Gabmax4/esp-webserver-battery-csv/Graficas bateria/Analis de las graficas/lectura-bateria.pdf

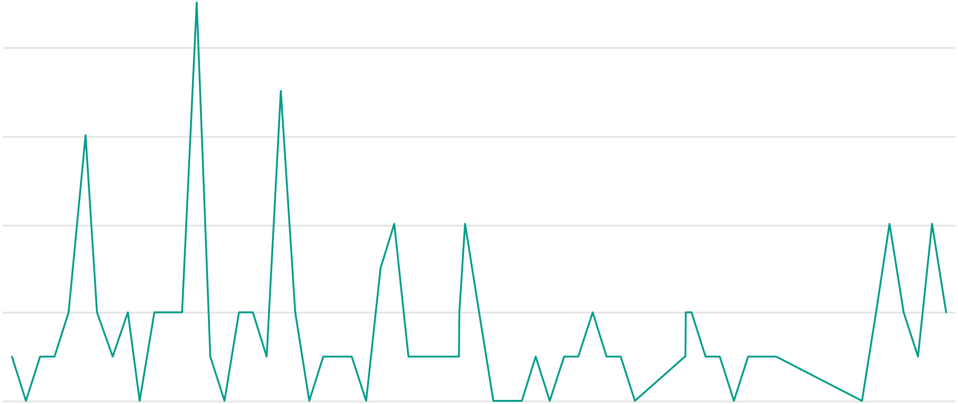
[picture p11: figure]

Tiempo

B

a

t

e

ria

## Lectura Bateria

22:43:30 | 22:43:45 | 22:44:00 | 22:44:15 | 22:44:30

616

618

620

622

624

626

628
