Gabmax4/esp-webserver-battery-csv/Graficas bateria/Carga de bateria/lectura-bateria (1).jpeg

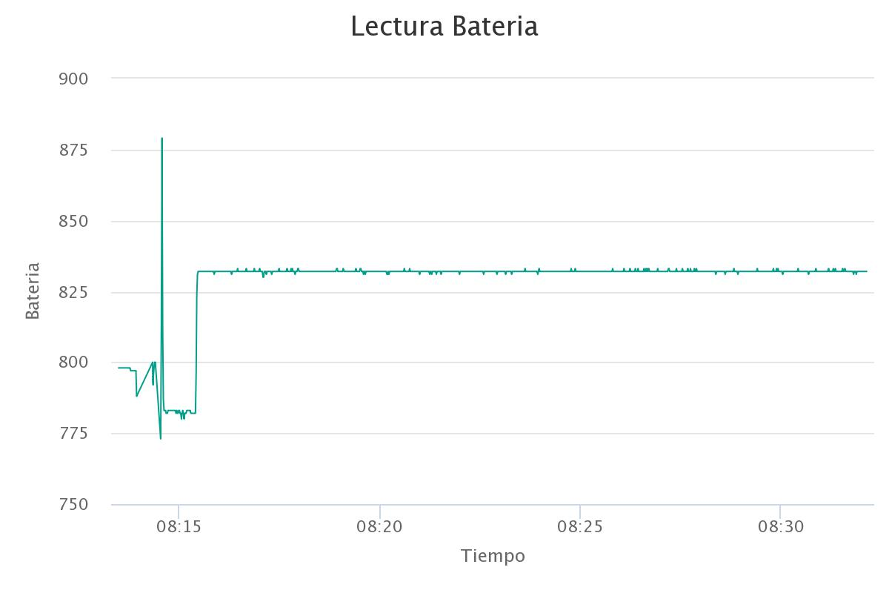
Graficas bateria/Carga de bateria/lectura-bateria (1).jpeg
