Gabmax4/esp-webserver-battery-csv/Graficas bateria/Carga de bateria/lectura-bateria.jpeg

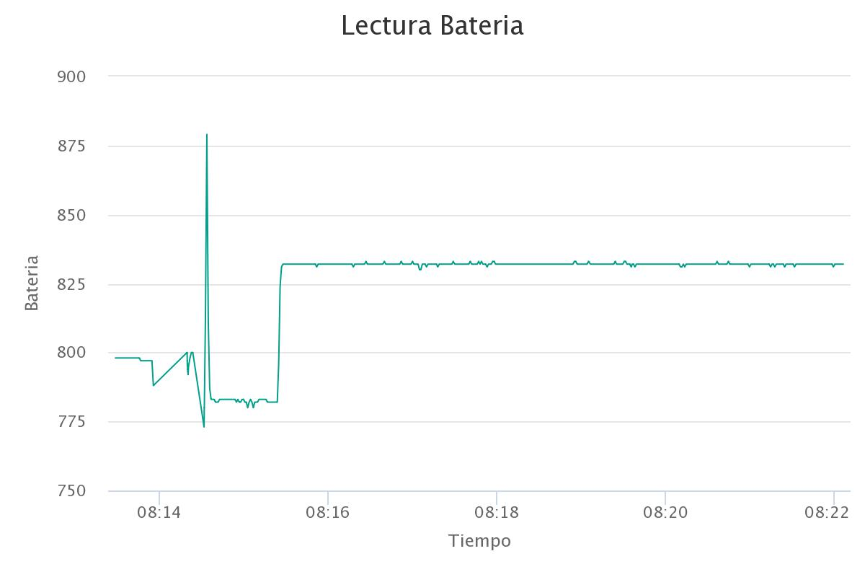
Graficas bateria/Carga de bateria/lectura-bateria.jpeg
