Gabmax4/esp-webserver-battery-csv/Simulacion 3D/Cargador-De-Pulseras.png

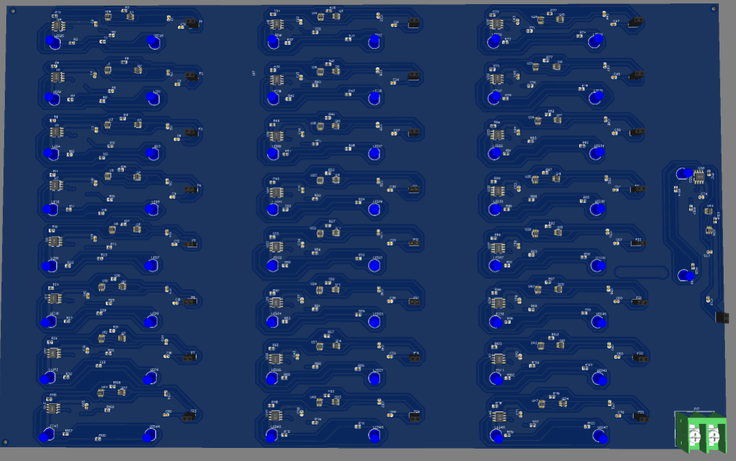
Simulacion 3D/Cargador-De-Pulseras.png
