Gabmax4/esp-webserver-battery-csv/Simulacion 3D/Escamatico-De-Pulsera.png

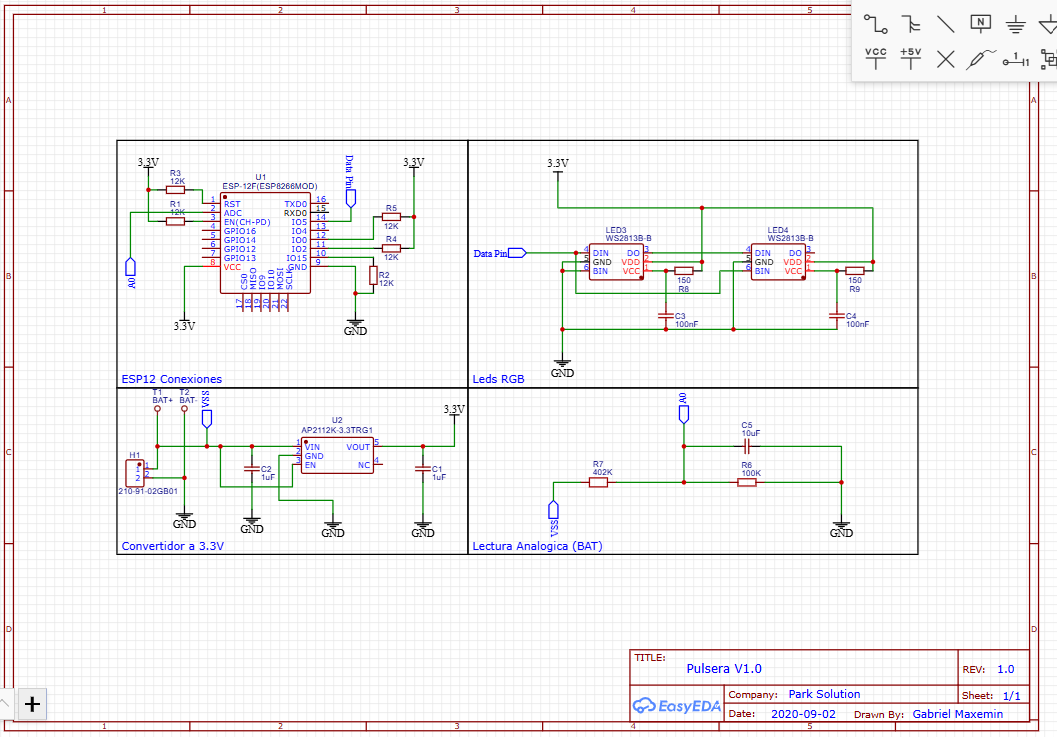
Simulacion 3D/Escamatico-De-Pulsera.png
