Gabmax4/esp-webserver-battery-csv/Simulacion 3D/WhatsApp Image 2019-08-04 at 23.47.41.jpeg

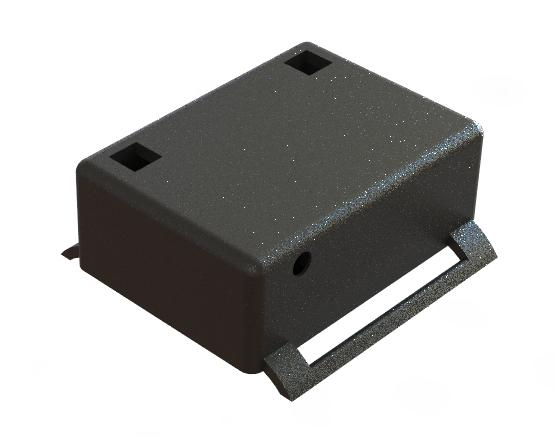
Simulacion 3D/WhatsApp Image 2019-08-04 at 23.47.41.jpeg
