Gabmax4/esp-webserver-battery-csv/Graficas bateria/Graficas de baterias (Pruebas)/Prueba No. 1/lectura-bateria (1).pdf

## Lectura Bateria

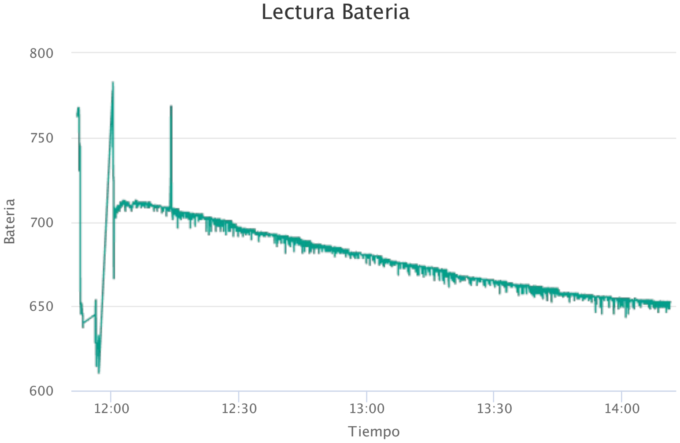
[picture p19: page 1]

Tiempo

B

a

t

e

ria

12:00 | 12:30 | 13:00 | 13:30 | 14:00

600

650

700

750

800
