Gabmax4/esp-webserver-battery-csv/Graficas bateria/Graficas de baterias (Pruebas)/Prueba No. 10/lectura-bateria (1).pdf

## Lectura Bateria

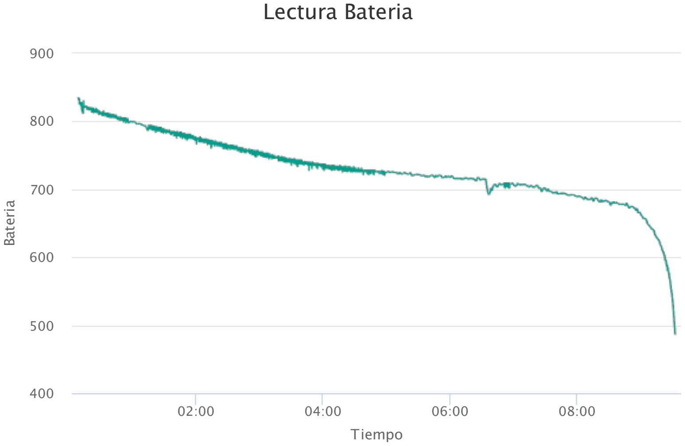
[picture p20: page 1]

Tiempo

B

a

t

e

ria

02:00 | 04:00 | 06:00 | 08:00

400

500

600

700

800

900
