Gabmax4/esp-webserver-battery-csv/Graficas bateria/Graficas de baterias (Pruebas)/Prueba No. 12/lectura-bateria (1).pdf

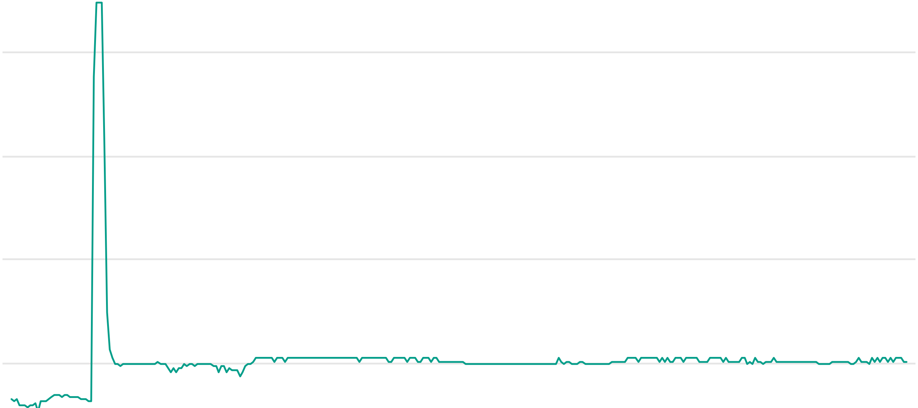
[picture p21: figure]

Tiempo

B

a

t

e

ria

## Lectura Bateria

08:01 | 08:02 | 08:03 | 08:04 | 08:05 | 08:06

800

850

900

950

1000

1050
