Gabmax4/esp-webserver-battery-csv/Graficas bateria/Graficas de baterias (Pruebas)/Prueba No. 12/lectura-bateria (2).pdf

## Lectura Bateria

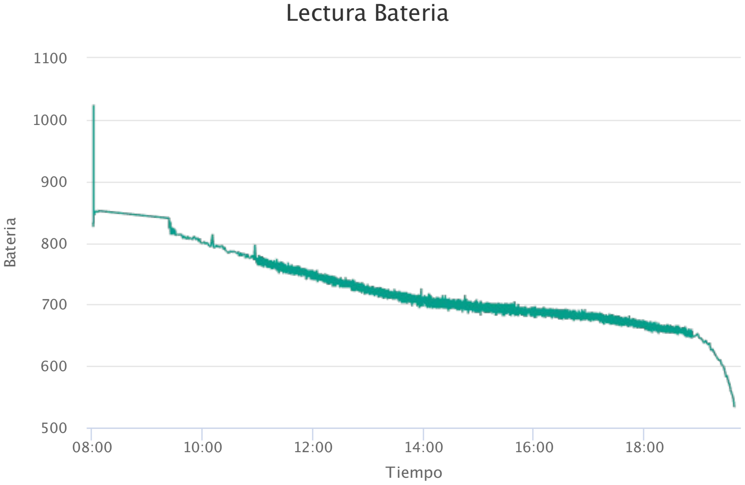
[picture p22: page 1]

Tiempo

B

a

t

e

ria

08:00 | 10:00 | 12:00 | 14:00 | 16:00 | 18:00

500

600

700

800

900

1000

1100
