Gabmax4/esp-webserver-battery-csv/Graficas bateria/Graficas de baterias (Pruebas)/Prueba No. 12/lectura-bateria (4).pdf

## Lectura Bateria

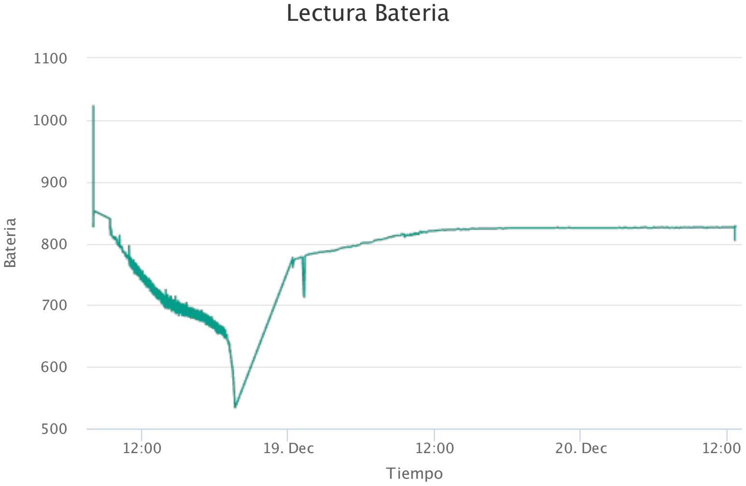
[picture p23: page 1]

Tiempo

B

a

t

e

ria

12:00 | 19. Dec | 12:00 | 20. Dec | 12:00

500

600

700

800

900

1000

1100
