Gabmax4/esp-webserver-battery-csv/Graficas bateria/Graficas de baterias (Pruebas)/Prueba No. 12/lectura-bateria (5).pdf

## Lectura Bateria

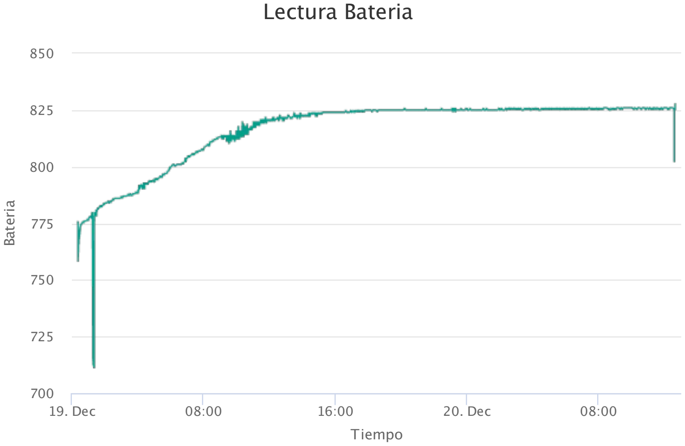
[picture p24: page 1]

Tiempo

B

a

t

e

ria

19. Dec | 08:00 | 16:00 | 20. Dec | 08:00

700

725

750

775

800

825

850
