Gabmax4/esp-webserver-battery-csv/Graficas bateria/Graficas de baterias (Pruebas)/Prueba No. 12/lectura-bateria (6).pdf

## Lectura Bateria

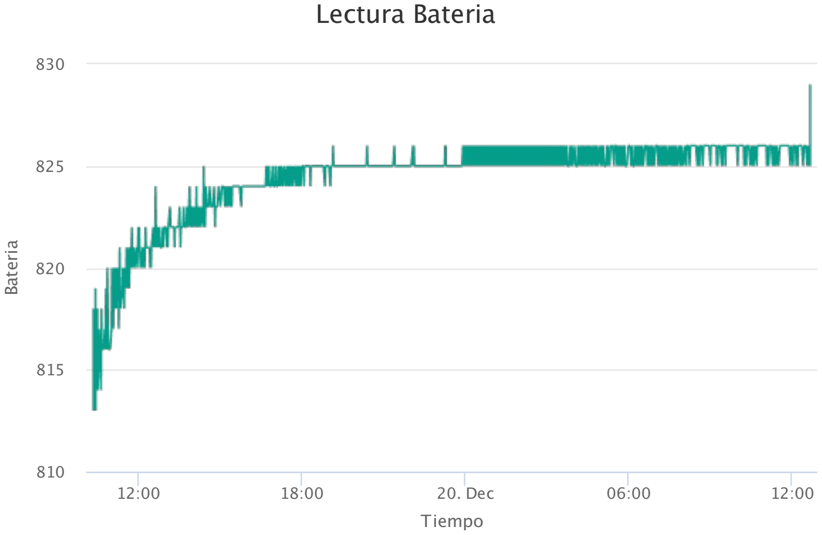
[picture p25: page 1]

Tiempo

B

a

t

e

ria

12:00 | 18:00 | 20. Dec | 06:00 | 12:00

810

815

820

825

830
