Gabmax4/esp-webserver-battery-csv/Graficas bateria/Graficas de baterias (Pruebas)/Prueba No. 12/lectura-bateria (7).pdf

## Lectura Bateria

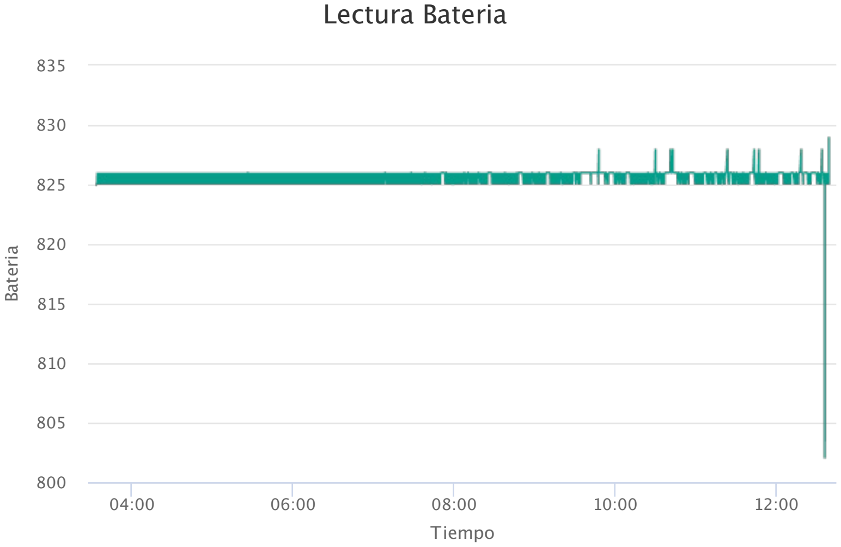
[picture p26: page 1]

Tiempo

B

a

t

e

ria

04:00 | 06:00 | 08:00 | 10:00 | 12:00

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
