Gabmax4/esp-webserver-battery-csv/Graficas bateria/Graficas de baterias (Pruebas)/Prueba No. 12/lectura-bateria (8).pdf

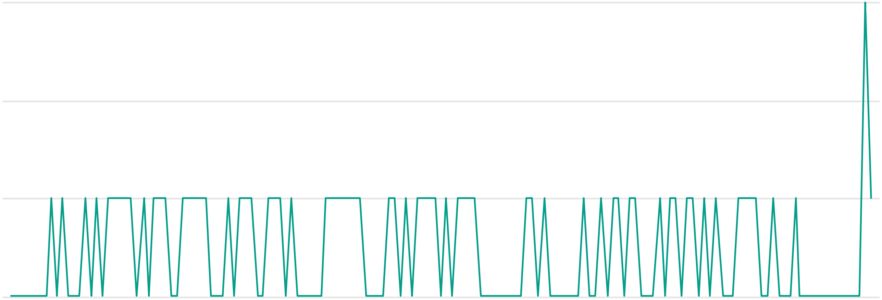
[picture p27: figure]

Tiempo

B

a

t

e

ria

## Lectura Bateria

12:37:00 | 12:37:30 | 12:38:00 | 12:38:30 | 12:39:00

824

825

826

827

828

829
