Gabmax4/esp-webserver-battery-csv/Graficas bateria/Graficas de baterias (Pruebas)/Prueba No. 12/lectura-bateria (9).pdf

## Lectura Bateria

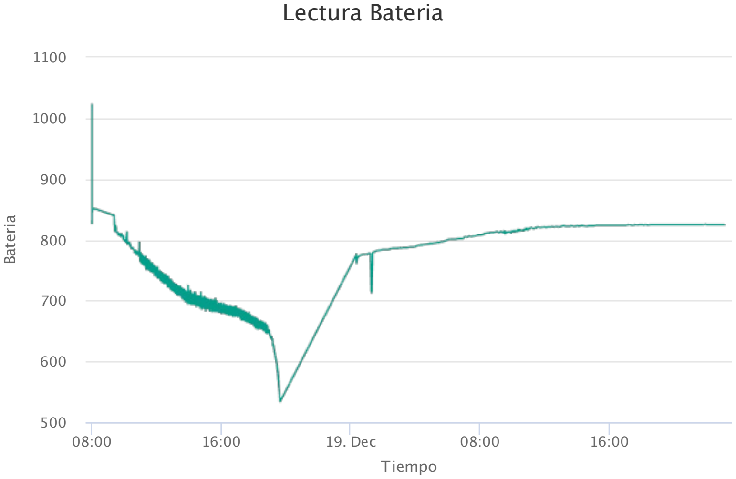
[picture p28: page 1]

Tiempo

B

a

t

e

ria

08:00 | 16:00 | 19. Dec | 08:00 | 16:00

500

600

700

800

900

1000

1100
