Gabmax4/esp-webserver-battery-csv/Graficas bateria/Graficas de baterias (Pruebas)/Prueba No. 3/lectura-bateria (1).pdf

## Lectura Bateria

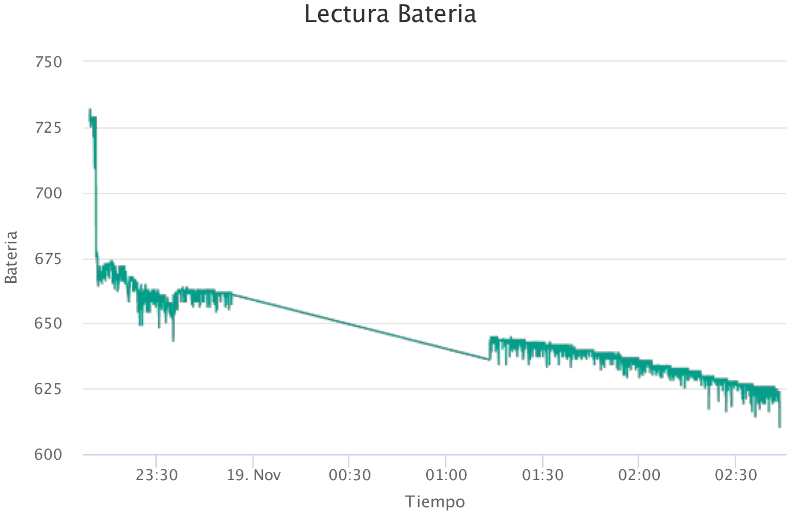
[picture p29: page 1]

Tiempo

B

a

t

e

ria

23:30 | 19. Nov | 00:30 | 01:00 | 01:30 | 02:00 | 02:30

600

625

650

675

700

725

750
