Gabmax4/esp-webserver-battery-csv/Graficas bateria/Graficas de baterias (Pruebas)/Prueba No. 4/lectura-bateria (1).pdf

## Lectura Bateria

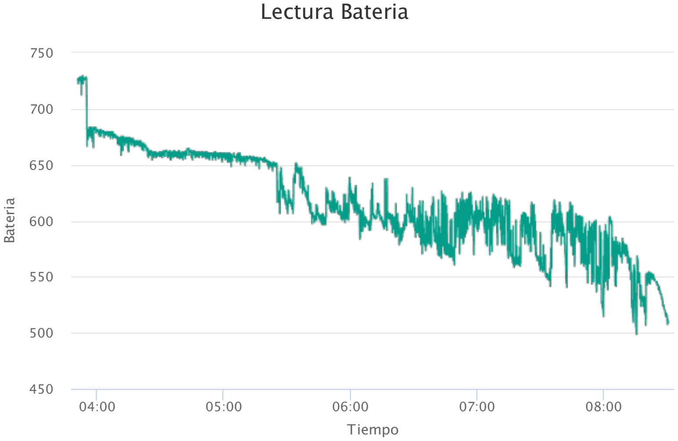
[picture p30: page 1]

Tiempo

B

a

t

e

ria

04:00 | 05:00 | 06:00 | 07:00 | 08:00

450

500

550

600

650

700

750
