Gabmax4/esp-webserver-battery-csv/Graficas bateria/Graficas de baterias (Pruebas)/Prueba No. 5/lectura-bateria (1).pdf

## Lectura Bateria

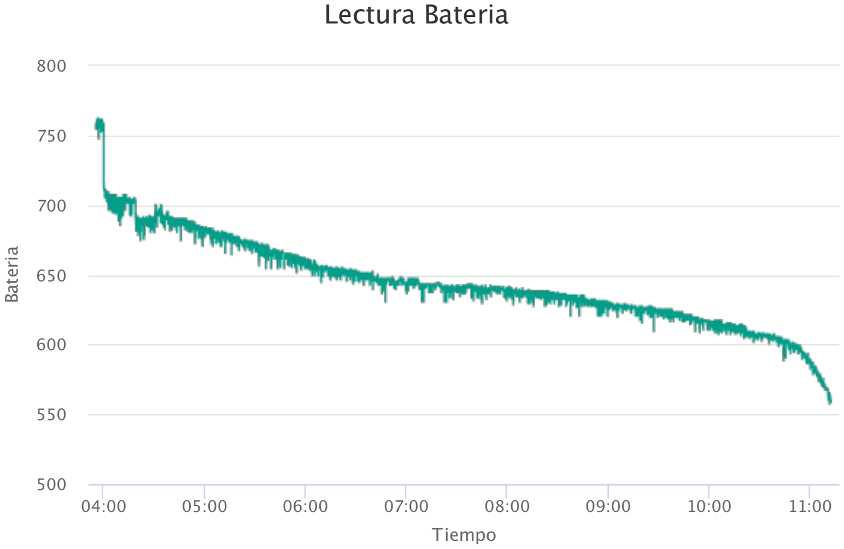
[picture p31: page 1]

Tiempo

B

a

t

e

ria

04:00 | 05:00 | 06:00 | 07:00 | 08:00 | 09:00 | 10:00 | 11:00

500

550

600

650

700

750

800
