Gabmax4/esp-webserver-battery-csv/Graficas bateria/Graficas de baterias (Pruebas)/Prueba No. 6/lectura-bateria (1).pdf

## Lectura Bateria

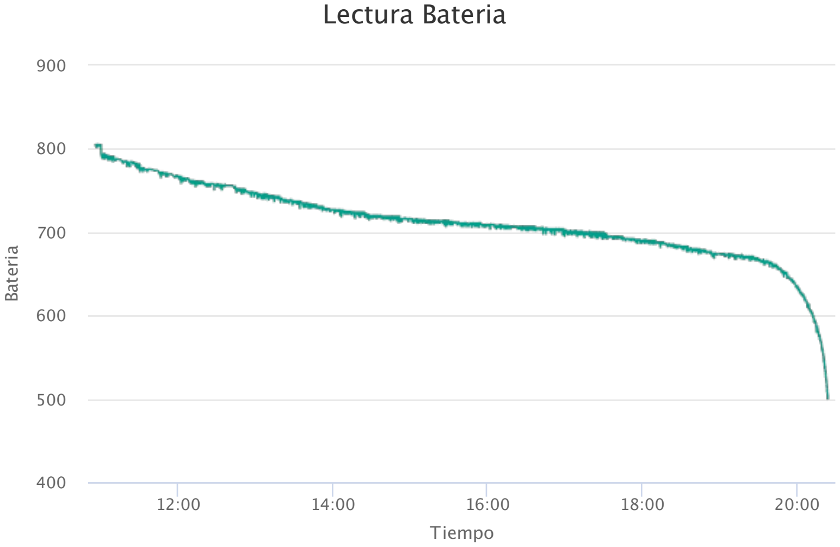
[picture p32: page 1]

Tiempo

B

a

t

e

ria

12:00 | 14:00 | 16:00 | 18:00 | 20:00

400

500

600

700

800

900
