Gabmax4/esp-webserver-battery-csv/Graficas bateria/Graficas de baterias (Pruebas)/Prueba No. 7/lectura-bateria (1).pdf

## Lectura Bateria

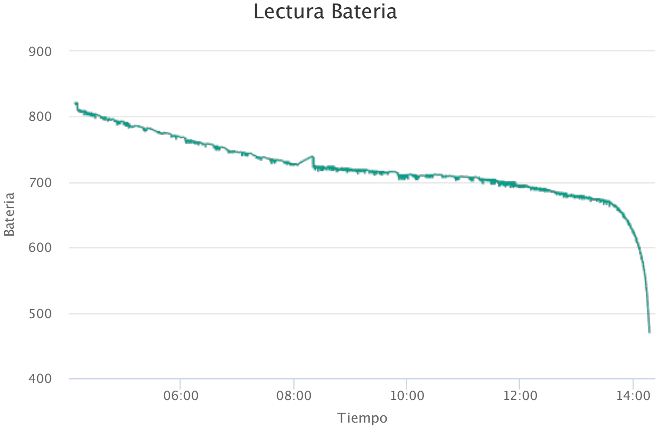
[picture p33: page 1]

Tiempo

B

a

t

e

ria

06:00 | 08:00 | 10:00 | 12:00 | 14:00

400

500

600

700

800

900
