Gabmax4/esp-webserver-battery-csv/Graficas bateria/Graficas de baterias (Pruebas)/Prueba No. 9/lectura-bateria (1).pdf

## Lectura Bateria

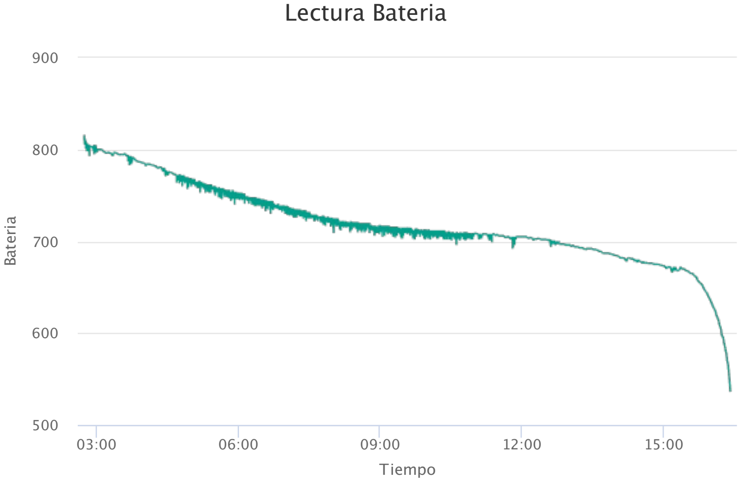
[picture p34: page 1]

Tiempo

B

a

t

e

ria

03:00 | 06:00 | 09:00 | 12:00 | 15:00

500

600

700

800

900
