Gabmax4/esp-webserver-battery-csv/Graficas bateria/Graficas de baterias (Pruebas)/Prueba No. 1/lectura-bateria (1).csv

Tiempo | Series 1
2020-11-16 11:51:56 | 762
2020-11-16 11:51:57 | 764
2020-11-16 11:51:58 | 765
2020-11-16 11:51:59 | 765
2020-11-16 11:52:00 | 765
2020-11-16 11:52:01 | 765
2020-11-16 11:52:02 | 763
2020-11-16 11:52:03 | 766
2020-11-16 11:52:04 | 766
2020-11-16 11:52:05 | 766
2020-11-16 11:52:06 | 766
2020-11-16 11:52:07 | 766
2020-11-16 11:52:08 | 766
2020-11-16 11:52:09 | 766
2020-11-16 11:52:10 | 766
2020-11-16 11:52:11 | 766
2020-11-16 11:52:12 | 766
2020-11-16 11:52:13 | 766
2020-11-16 11:52:14 | 766
2020-11-16 11:52:15 | 768
2020-11-16 11:52:16 | 766
2020-11-16 11:52:17 | 766
2020-11-16 11:52:18 | 766
2020-11-16 11:52:19 | 768
2020-11-16 11:52:20 | 768
2020-11-16 11:52:21 | 768
2020-11-16 11:52:22 | 763
2020-11-16 11:52:23 | 730
2020-11-16 11:52:24 | 734
2020-11-16 11:52:25 | 739
2020-11-16 11:52:26 | 739
2020-11-16 11:52:27 | 746
2020-11-16 11:52:28 | 747
2020-11-16 11:52:29 | 746
2020-11-16 11:52:30 | 739
2020-11-16 11:52:31 | 741
2020-11-16 11:52:32 | 745
2020-11-16 11:52:33 | 745
2020-11-16 11:52:34 | 745
2020-11-16 11:52:35 | 745
2020-11-16 11:52:36 | 744
2020-11-16 11:52:37 | 745
2020-11-16 11:52:38 | 677
2020-11-16 11:52:39 | 656
2020-11-16 11:52:40 | 651
2020-11-16 11:52:41 | 653
2020-11-16 11:52:42 | 653
2020-11-16 11:52:43 | 652
2020-11-16 11:52:44 | 651
2020-11-16 11:52:45 | 649
2020-11-16 11:52:46 | 648
2020-11-16 11:52:47 | 645
2020-11-16 11:52:48 | 648
2020-11-16 11:52:49 | 649
2020-11-16 11:52:50 | 648
2020-11-16 11:52:51 | 648
2020-11-16 11:52:52 | 652
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
2020-11-16 12:59:58 | 680
2020-11-16 12:59:59 | 681
2020-11-16 13:00:00 | 680
2020-11-16 13:00:01 | 681
2020-11-16 13:00:02 | 681
2020-11-16 13:00:03 | 681
2020-11-16 13:00:04 | 681
2020-11-16 13:00:05 | 681
2020-11-16 13:00:06 | 681
2020-11-16 13:00:07 | 681
2020-11-16 13:00:08 | 681
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
