Gabmax4/esp-webserver-battery-csv/Graficas bateria/Graficas de baterias (Pruebas)/Prueba No. 10/lectura-bateria (1).csv

Tiempo | Series 1
2020-12-01 00:08:23 | 835
2020-12-01 00:08:24 | 835
2020-12-01 00:08:25 | 835
2020-12-01 00:08:26 | 835
2020-12-01 00:08:27 | 835
2020-12-01 00:08:28 | 835
2020-12-01 00:08:29 | 835
2020-12-01 00:08:30 | 835
2020-12-01 00:08:31 | 835
2020-12-01 00:08:32 | 835
2020-12-01 00:08:33 | 835
2020-12-01 00:08:34 | 835
2020-12-01 00:08:35 | 835
2020-12-01 00:08:36 | 835
2020-12-01 00:08:37 | 835
2020-12-01 00:08:38 | 834
2020-12-01 00:08:39 | 835
2020-12-01 00:08:40 | 835
2020-12-01 00:08:41 | 835
2020-12-01 00:08:42 | 835
2020-12-01 00:08:43 | 835
2020-12-01 00:08:44 | 835
2020-12-01 00:08:45 | 835
2020-12-01 00:08:46 | 835
2020-12-01 00:08:47 | 835
2020-12-01 00:08:48 | 835
2020-12-01 00:08:49 | 835
2020-12-01 00:08:50 | 835
2020-12-01 00:08:51 | 835
2020-12-01 00:08:52 | 835
2020-12-01 00:08:53 | 835
2020-12-01 00:08:54 | 835
2020-12-01 00:08:55 | 835
2020-12-01 00:08:56 | 834
2020-12-01 00:08:57 | 835
2020-12-01 00:08:58 | 835
2020-12-01 00:08:59 | 834
2020-12-01 00:09:00 | 835
2020-12-01 00:09:01 | 835
2020-12-01 00:09:02 | 835
2020-12-01 00:09:03 | 835
2020-12-01 00:09:04 | 835
2020-12-01 00:09:05 | 835
2020-12-01 00:09:06 | 835
2020-12-01 00:09:07 | 835
2020-12-01 00:09:08 | 835
2020-12-01 00:09:09 | 834
2020-12-01 00:09:10 | 835
2020-12-01 00:09:11 | 833
2020-12-01 00:09:12 | 834
2020-12-01 00:09:13 | 834
2020-12-01 00:09:14 | 834
2020-12-01 00:09:15 | 835
2020-12-01 00:09:16 | 834
2020-12-01 00:09:17 | 834
2020-12-01 00:09:18 | 835
2020-12-01 00:09:19 | 834
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
2020-12-01 01:34:21 | 784
2020-12-01 01:34:22 | 784
2020-12-01 01:34:23 | 783
2020-12-01 01:34:24 | 784
2020-12-01 01:34:25 | 785
2020-12-01 01:34:26 | 784
2020-12-01 01:34:27 | 784
2020-12-01 01:34:28 | 783
2020-12-01 01:34:29 | 785
2020-12-01 01:34:30 | 785
2020-12-01 01:34:31 | 786
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
