Gabmax4/esp-webserver-battery-csv/Graficas bateria/Graficas de baterias (Pruebas)/Prueba No. 11/lectura-bateria (1).csv

Tiempo | Series 1
2020-12-07 07:56:48 | 853
2020-12-07 07:56:49 | 852
2020-12-07 07:56:50 | 853
2020-12-07 07:56:51 | 853
2020-12-07 07:56:52 | 854
2020-12-07 07:56:53 | 855
2020-12-07 07:56:54 | 855
2020-12-07 07:56:55 | 855
2020-12-07 07:56:56 | 855
2020-12-07 07:56:57 | 855
2020-12-07 07:56:58 | 855
2020-12-07 07:56:59 | 855
2020-12-07 07:57:00 | 855
2020-12-07 07:57:01 | 855
2020-12-07 07:57:02 | 855
2020-12-07 07:57:03 | 855
2020-12-07 07:57:04 | 855
2020-12-07 07:57:05 | 855
2020-12-07 07:57:06 | 855
2020-12-07 07:57:07 | 855
2020-12-07 07:57:08 | 856
2020-12-07 07:57:09 | 856
2020-12-07 07:57:10 | 855
2020-12-07 07:57:11 | 855
2020-12-07 07:57:12 | 855
2020-12-07 07:57:13 | 855
2020-12-07 07:57:14 | 855
2020-12-07 07:57:15 | 855
2020-12-07 07:57:16 | 855
2020-12-07 07:57:17 | 855
2020-12-07 07:57:18 | 855
2020-12-07 07:57:19 | 855
2020-12-07 07:57:20 | 855
2020-12-07 07:57:21 | 855
2020-12-07 07:57:22 | 855
2020-12-07 07:57:23 | 855
2020-12-07 07:57:24 | 855
2020-12-07 07:57:25 | 855
2020-12-07 07:57:26 | 855
2020-12-07 07:57:27 | 855
2020-12-07 07:57:28 | 855
2020-12-07 07:57:29 | 855
2020-12-07 07:57:30 | 855
2020-12-07 07:57:31 | 855
2020-12-07 07:57:32 | 855
2020-12-07 07:57:33 | 855
2020-12-07 07:57:34 | 855
2020-12-07 07:57:35 | 855
2020-12-07 07:57:36 | 855
2020-12-07 07:57:37 | 855
2020-12-07 07:57:38 | 855
2020-12-07 07:57:39 | 855
2020-12-07 07:57:40 | 855
2020-12-07 07:57:41 | 855
2020-12-07 07:57:42 | 855
2020-12-07 07:57:43 | 855
2020-12-07 07:57:44 | 855
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
2020-12-07 09:16:48 | 811
2020-12-07 09:16:49 | 812
2020-12-07 09:16:50 | 811
2020-12-07 09:16:51 | 811
2020-12-07 09:16:52 | 812
2020-12-07 09:16:53 | 813
2020-12-07 09:16:54 | 811
2020-12-07 09:16:55 | 811
2020-12-07 09:16:56 | 811
2020-12-07 09:16:57 | 812
2020-12-07 09:16:58 | 808
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
