Gabmax4/esp-webserver-battery-csv/Graficas bateria/Graficas de baterias (Pruebas)/Prueba No. 7/lectura-bateria.jpeg

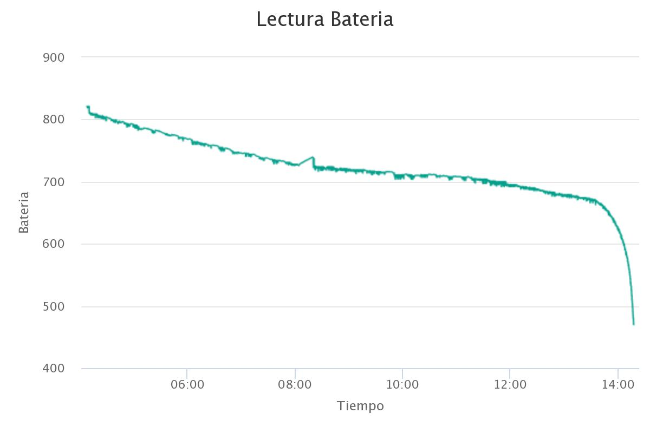
Graficas bateria/Graficas de baterias (Pruebas)/Prueba No. 7/lectura-bateria.jpeg
