Gabmax4/esp-webserver-battery-csv/Graficas bateria/Graficas de baterias (Pruebas)/Prueba No. 12/lectura-bateria (9).jpeg

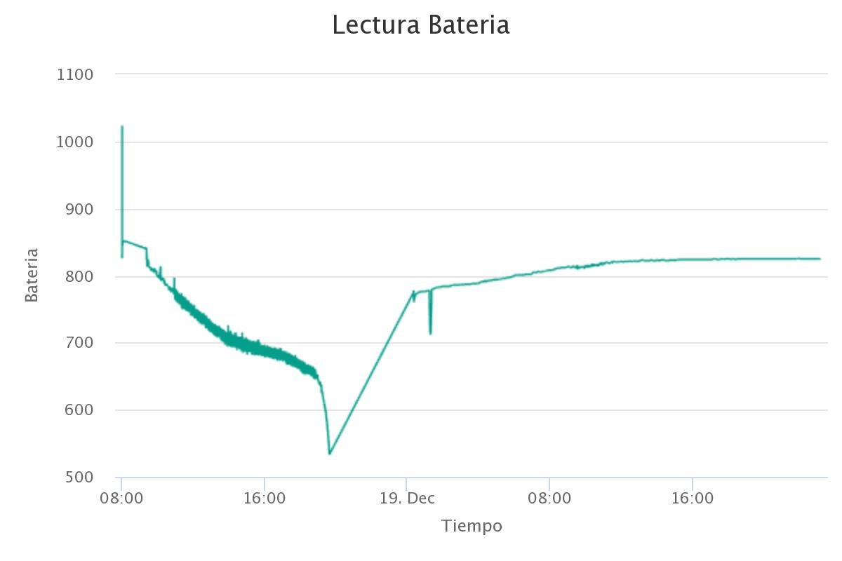
Graficas bateria/Graficas de baterias (Pruebas)/Prueba No. 12/lectura-bateria (9).jpeg
