Gabmax4/esp-webserver-battery-csv/Pulseras PCB/PCB_1/Diagram Wrisband.pdf

## GND

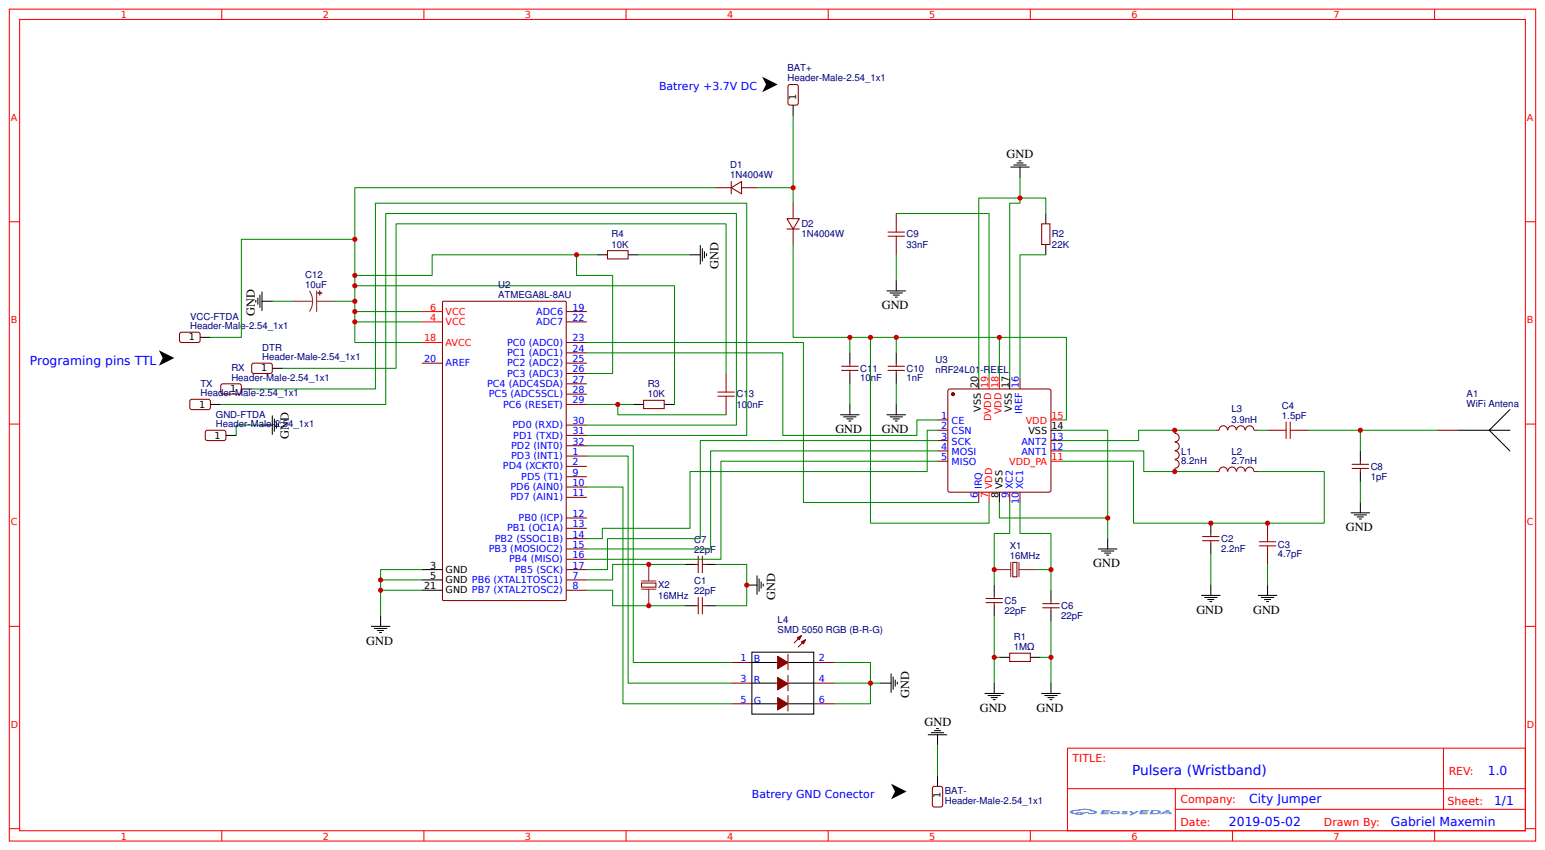
[picture p52: page 1]

VDD_PA 11 ANT1 12 ANT2 13 VSS 14 VDD 15 IREF 16 VSS 17

Drawn By: Gabriel Maxemin
