Gabmax4/esp-webserver-battery-csv/Graficas bateria/Graficas de baterias (Pruebas)/Prueba No. 2/lectura-bateria (1).pdf

## Lectura Bateria

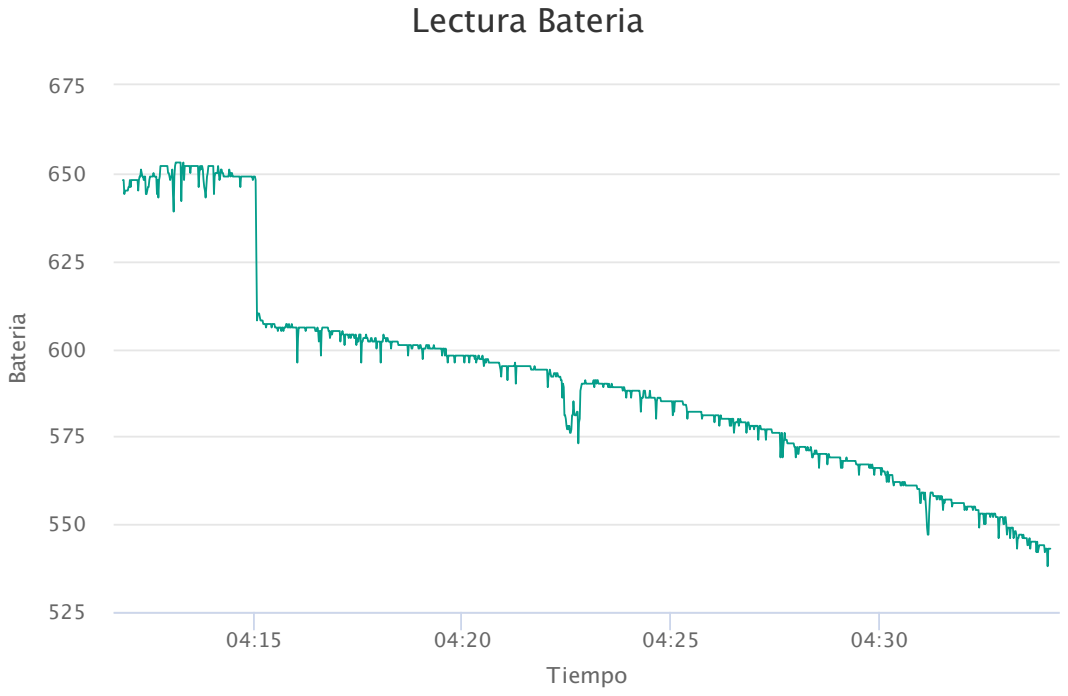
[picture p55: page 1]
Tiempo; ria
