Gabmax4/esp-webserver-battery-csv/Graficas bateria/Carga de bateria/lectura-bateria (1).pdf

## Lectura Bateria

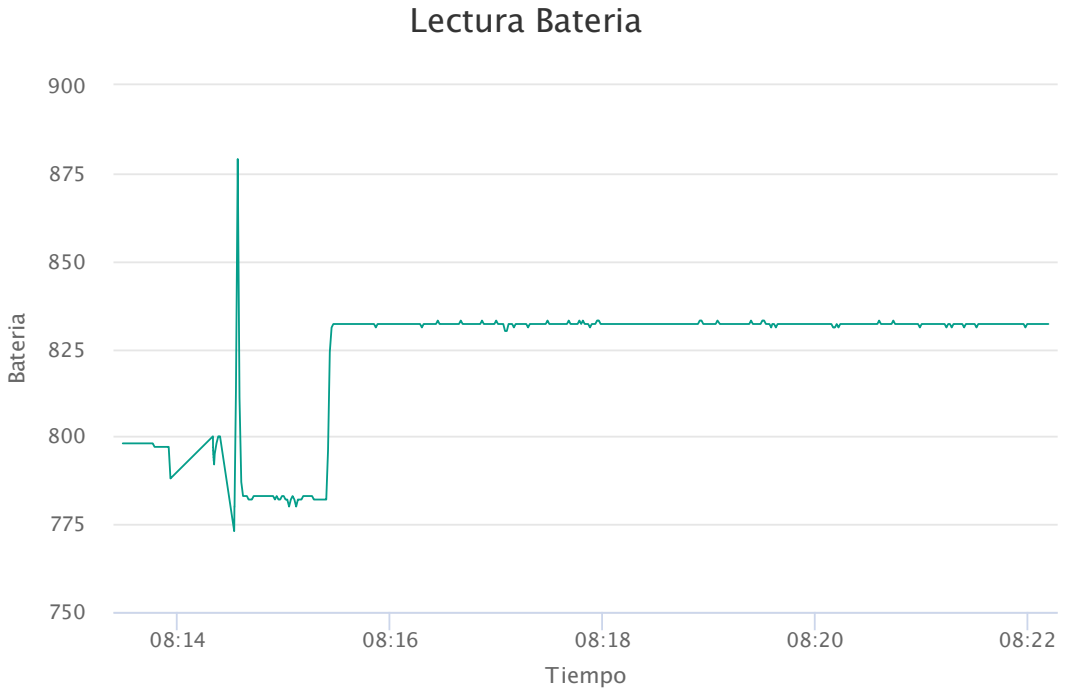
[picture p56: page 1]
Tiempo; ria
