Gabmax4/esp-webserver-battery-csv/Graficas bateria/Carga de bateria/lectura-bateria (2).pdf

## Lectura Bateria

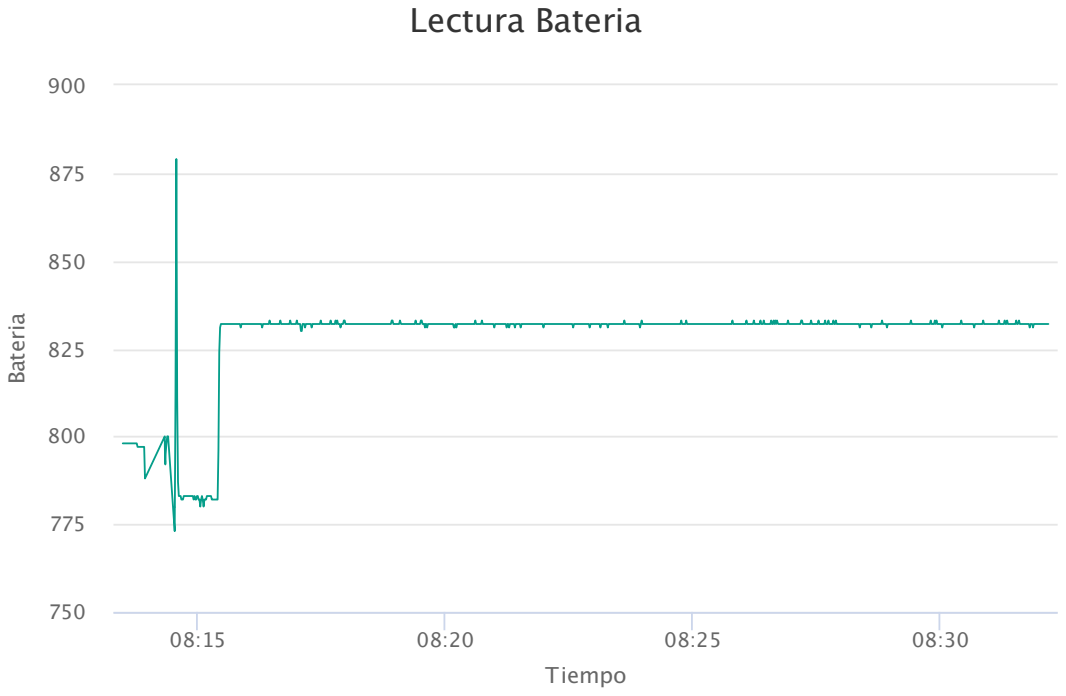
[picture p57: page 1]
Tiempo; ria
