Gabmax4/esp-webserver-battery-csv/Pulseras PCB/PCB_1/19cbe7b8-5e96-4131-a5ab-255a23e25a84.pdf

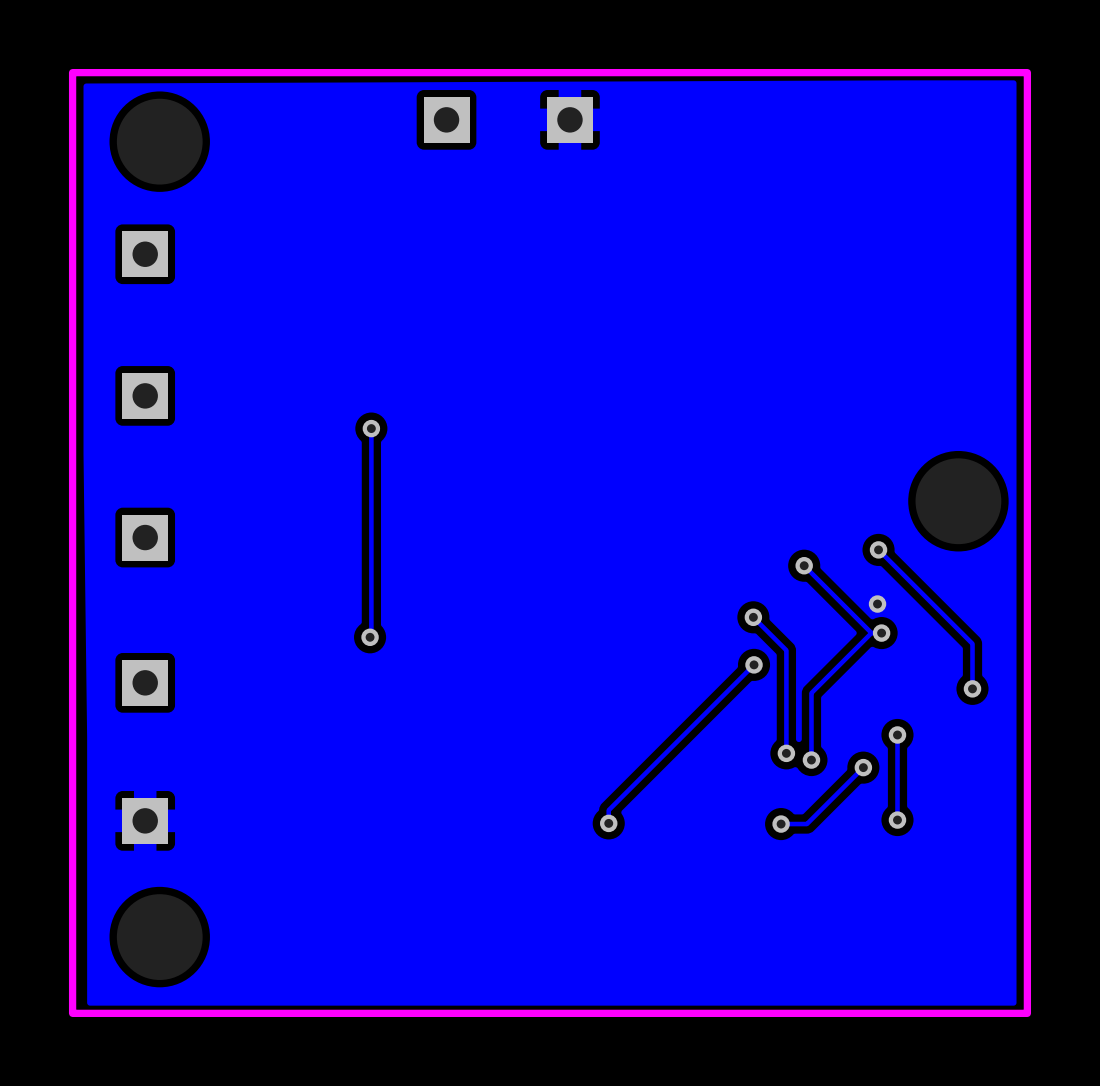
[picture p58: page 1]
