Gabmax4/esp-webserver-battery-csv/Pulseras PCB/PCB_1/45ad427b-9e12-4d07-8082-afed4b52ff00.pdf

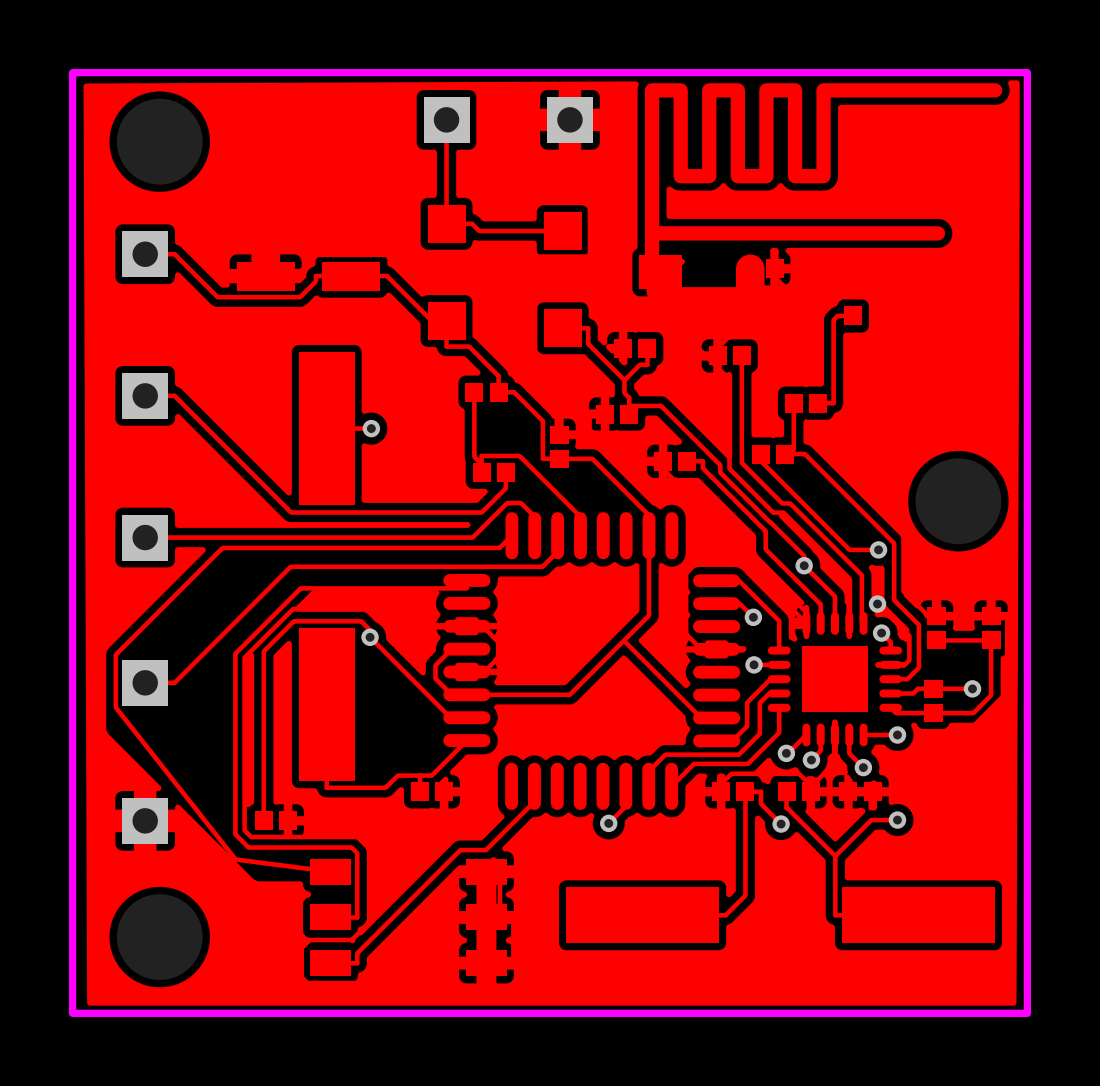
[picture p59: page 1]
