Gabmax4/esp-webserver-battery-csv/Pulseras PCB/PCB_1/846a0991-e67d-45aa-9feb-4397b182c37f.pdf

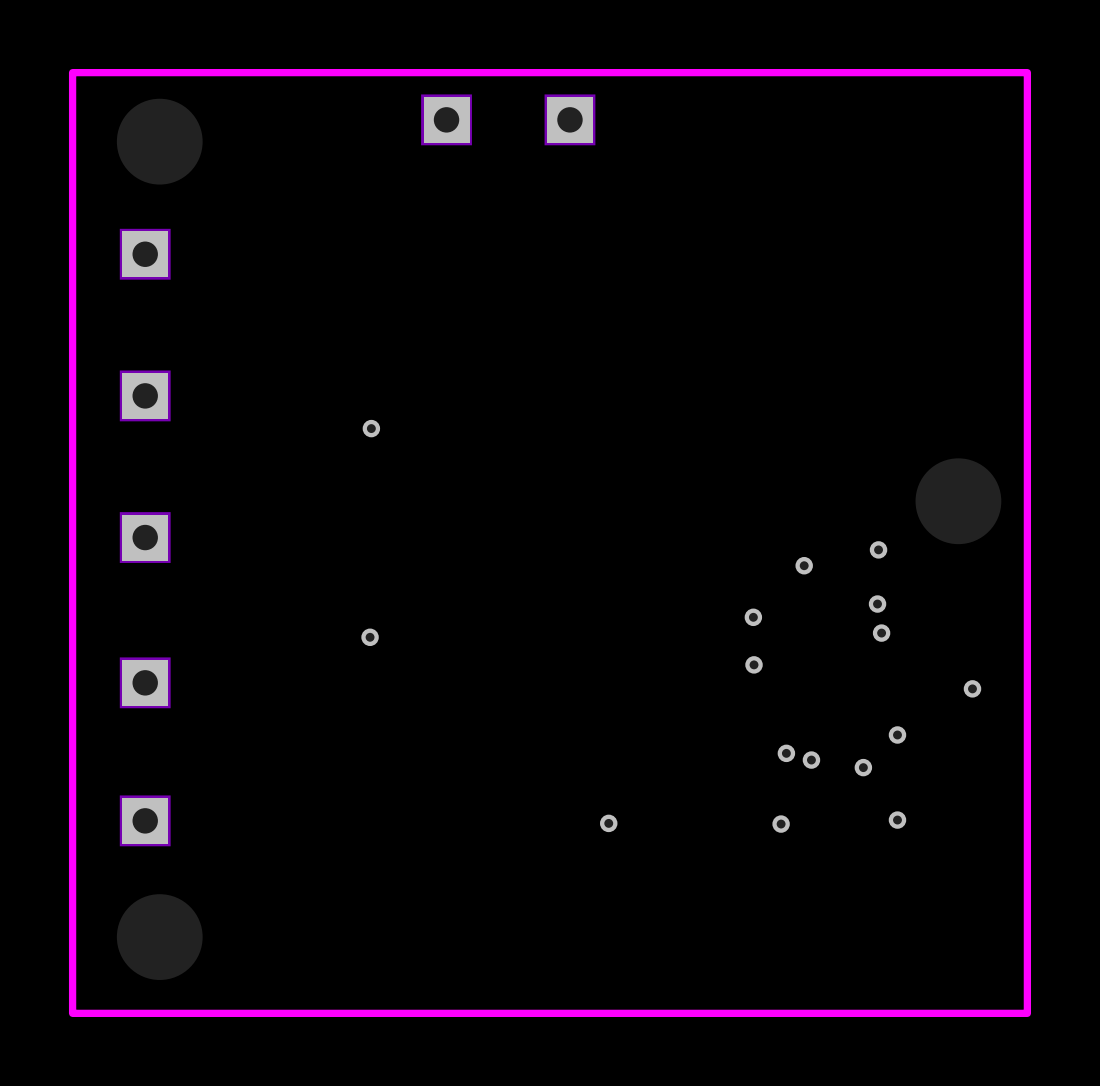
[picture p60: page 1]
