Gabmax4/esp-webserver-battery-csv/Pulseras PCB/PCB_1/PCB_pcb_20190503223241.pdf

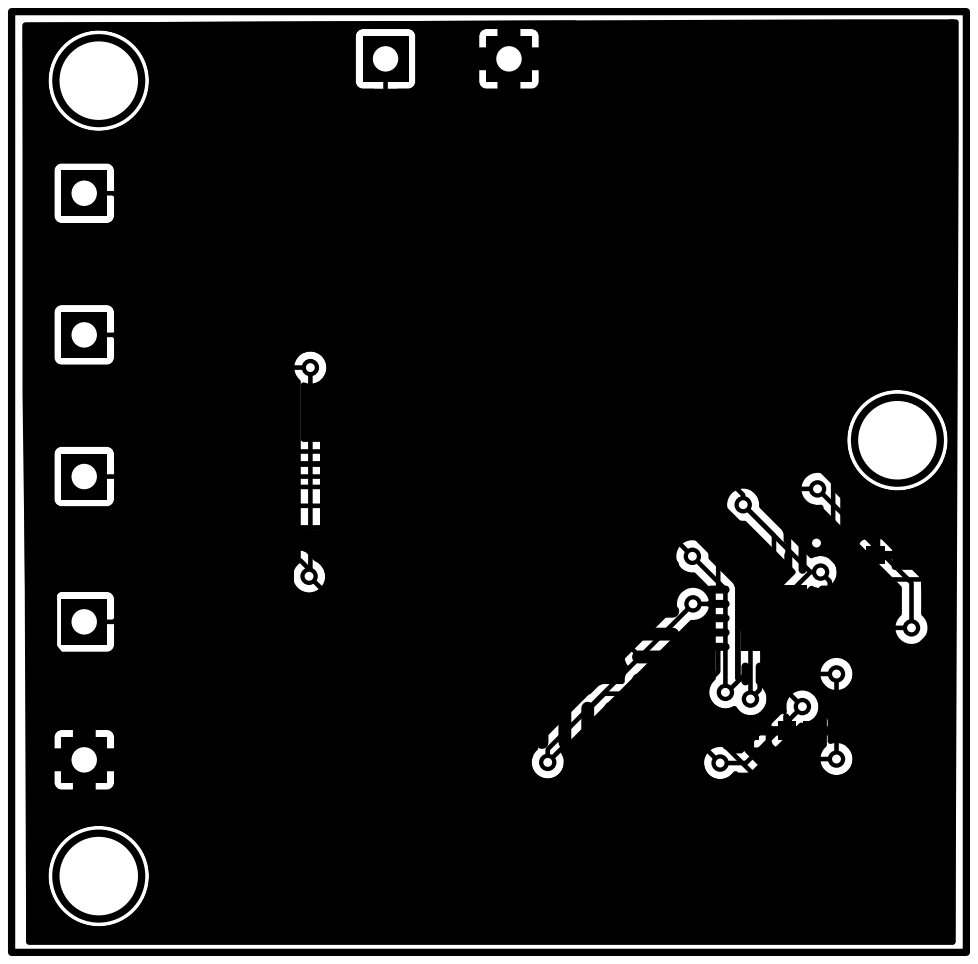
[picture p61: page 1]
